P0ed/5Y-Mission/Modules/Fn.asc

C1: Cap; 47p
C2: Cap; 47p
C3: Cap; 47p
C4: Cap; 47p
C5: Cap; 47p
C6: Cap; 47p
C9: Cap; 47p
CF: Cap; 4n7
D1: LED; QTLP690C
D2: LED; QTLP690C
FF: voltage; -4
FFA: voltage; 0
FRA: voltage; 0
PULS: voltage; PULSE(0 5 0 0.00001 0.00001 0.001 0.02 4)
R1: Res; 47K
R2: Res; 47K
R3: res; 100K
R4: Res; 4K7
R5: Res; 47K
R6: Res; 47K
R7: Res; 4K7
R8: Res; 100K
R9: Res; 68K
R10: Res; 6Meg8
R11: Res; 68K
R12: Res; 150K
R13: Res; 68K
R14: Res; 470
R15: Res; 100K
R16: Res; 68K
R17: Res; 150K
R18: Res; 68K
R19: Res; 150K
R20: Res; 68K
R21: Res; 10K
R22: Res; 680K
R23: Res; 100K
R24: Res; 100K
R25: res; 4K7
R26: Res; 47K
R27: Res; 22K
R28: Res; 100K
R29: Res; 470
R30: Res; 68K
R31: Res; 150K
R32: Res; 150K
R33: Res; 680K
R34: Res; 100K
R35: Res; 33K
R36: Res; 47K
R37: Res; 470
R38: Res; 47K
R39: Res; 68K
R40: Res; 100K
R41: Res; 4K7
R42: Res; 47K
R44: res; 680K
R45: res; 680K
R46: res; 100K
R47: Res; 470
R48: Res; 100K
R49: Res; 100K
R50: Res; 4K7
R51: Res; 100K
R52: Res; 68K
R54: Res; 33K
R55: Res; 91K
R56: Res; 150K
R57: Res; 150K
R58: Res; 680K
R59: Res; 680K
R60: Res; 4K7
R61: Res; 68K
R62: Res; 91K
R63: Res; 4K7
R64: Res; 91K
R65: Res; 4K7
R66: Res; 91K
R67: Res; 68K
R68: Res; 9K1
R69: Res; 9K1
R70: Res; 9K1
R71: Res; 9K1
R73: Res; 100K
R74: Res; 680K
R75: Res; 4K7
R77: Res; 680K
R78: Res; 4K7
R79: Res; 6Meg8
SAW: voltage; PULSE(0 5 0 0.005 0.005 0 0.01)
SINE: voltage; SINE(2 4 240 0 0)
U1/1: AD823A
U1/2: AD823A
U1: AD823A
U2/1: AD823A
U2/2: AD823A
U3/2: AD823A
U4/1: AD823A
U4/2: AD823A
U5/1: AD823A
U5/2: AD823
U6/1: AD823A
U6/2: AD823
U7/1: AD823A
U7/2: AD823
U8/1: AD823A
U8/2: AD823A
U9/1: AD823A
U9/2: AD823A
U10/1: AD823A
U10/2: AD823A
U11/1: AD823A
U11/2: AD823A
U12/1: dflop; Vhigh=11.95 Vlow=0.05 Trise=0.0000002 Tfall=0.0000002
U12/2: dflop; Vhigh=11.95 Vlow=0.05 Trise=0.0000002 Tfall=0.0000002
U14/1: npn; BC847A
U14/2: npn; BC847A
U15/1: pnp; BC857A
U15/2: pnp; BC857A
V5: voltage; 5
V+: voltage; PULSE(0 12 0 0.00001 0 220)
V-: voltage; PULSE(0 -12 0 0.00001 0 220)
Z1: ADR5045
Named nets: LP, V+, V-, SAW, END, _VRF, 0, VFF, TRIG, LPO, _ATK, DEK, _DEK, ATK, LIM, VRF, RISEP, REF, SW21, FREQ, SW13, SW11, PULS, FALLP, SW23, _VFF, SINE, _LPO, LIMO, RISEAP, FALLAP, RISEIN, FALLIN, SW12, SW22, DATA, _REF, LPB, SIG, TBTN, ENDO, _FREQ
.tran 68ms
