P0ed/5Y-Mission/Modules/Function.asc

C1: Cap; 47p
C2: Cap; 47p
C3: Cap; 47p
C4: Cap; 47p
C5: Cap; 47p
C9: Cap; 47p
C11: Cap; 47p
CF: Cap; 10n
FF: voltage; 0
FFA: voltage; 0
FR: voltage; 5
FRA: voltage; 0
PULS: voltage; PULSE(.034 5.4 0.1 0 0 0.01 0.2 2)
Q1: npn; MAT-02
Q2: npn; MAT-02
Q3: npn; MAT-02
Q4: npn; MAT-02
R2: Res; 51K
R3: Res; 100K
R4: Res; 5K4
R5: Res; 51K
R6: Res; 51K
R7: Res; 5K4
R8: Res; 200K
R9: Res; 110K
R10: Res; 910K
R11: Res; 110K
R12: Res; 200K
R13: Res; 5K4
R14: Res; 51K
R15: Res; 200K
R16: Res; 51K
R17: Res; 51K
R18: Res; 5K4
R19: Res; 68K
R20: Res; 51K
R21: Res; 15K
R22: Res; 200K
R23: Res; 200K
R24: Res; 200K
R25: Res; 200K
R26: Res; 51K
R27: Res; 20K
R28: Res; 51K
R29: Res; 470
R30: Res; 110K
R31: Res; 200K
R32: Res; 200K
R33: Res; 4K7
R34: Res; 100K
R35: Res; 51K
R36: Res; 15K
R37: Res; 51K
R38: Res; 910K
R39: Res; 110K
R40: Res; 470
R41: Res; 4K7
R42: Res; 15K
R43: Res; 51K
R44: Res; 15K
R47: Res; 51K
R48: Res; 100K
R49: Res; 910K
R51: Res; 51K
R52: Res; 51K
R53: Res; 68K
R54: Res; 51K
R55: Res; 910K
R56: Res; 20K
R57: Res; 4K7
R58: Res; 4K7
R59: Res; 4Meg4
REF: voltage; 5
RPOT: Res; 50K
SAW: voltage; PULSE(0 5.2 0 0.025 0.025 0 0.05)
SINE: voltage; SINE(2 4 240 0 0)
U1/1: AD823A
U1/2: AD823A
U2/1: AD823A
U2/2: AD823A
U3/1: AD823A
U3/2: AD823
U4/1: AD823A
U4/2: AD823
U5/1: AD823
U5/2: AD823A
U6/1: AD823A
U6/2: AD823
U7/1: AD823A
U7/2: AD823
U8: ADG419
U9/1: dflop; Vhigh=11.95 Vlow=0.05 Trise=0.0000002 Tfall=0.0000002
U9/2: dflop; Vhigh=11.95 Vlow=0.05 Trise=0.0000002 Tfall=0.0000002
V+: voltage; 12
V-: voltage; -12
Z1: ADR5045
Named nets: LP, V+, V-, SAW, END, _VRF, VRF, _VFF, VFF, 0, ENDO, TRIG, LPO, F1, _ATK, _DEK, DEK, ATK, _END, VTRIG, SIG, SIG_IN, HOLD, REF, SW21, F4, SW13, SW11, FREQ, PULS, SW23, INTD, INT, SINE, POS, NEG
.tran 64s
